blecube/PCB-Design/images/PCB Design - Adapter Card - Copper Top.png

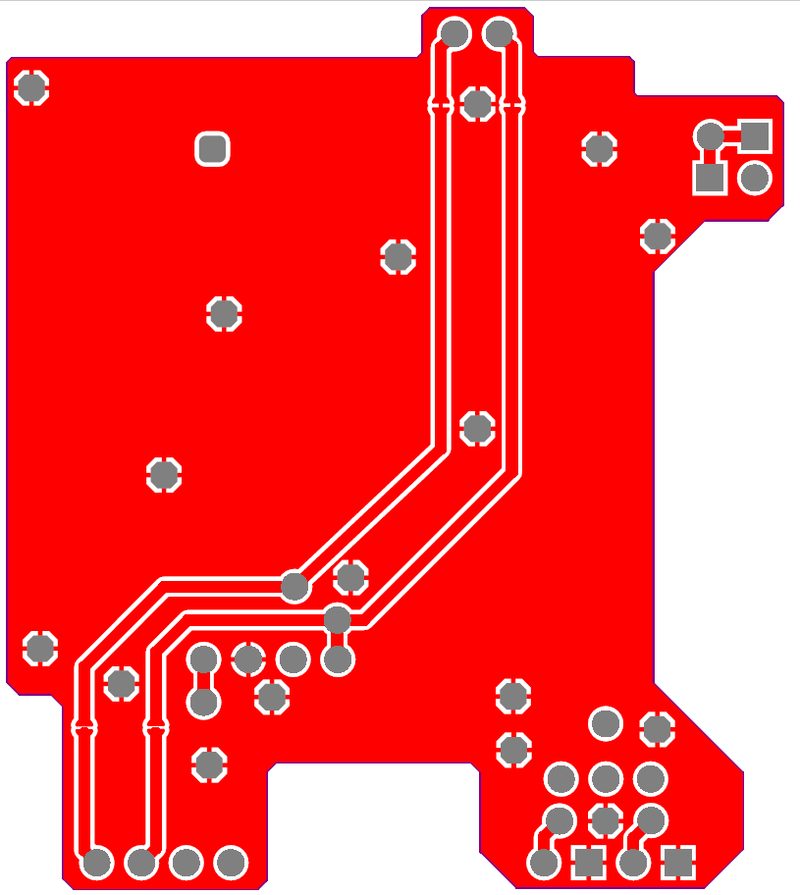
images/PCB Design - Adapter Card - Copper Top.png
