blecube/PCB-Design/images/PCB Design - Adapter Card.png

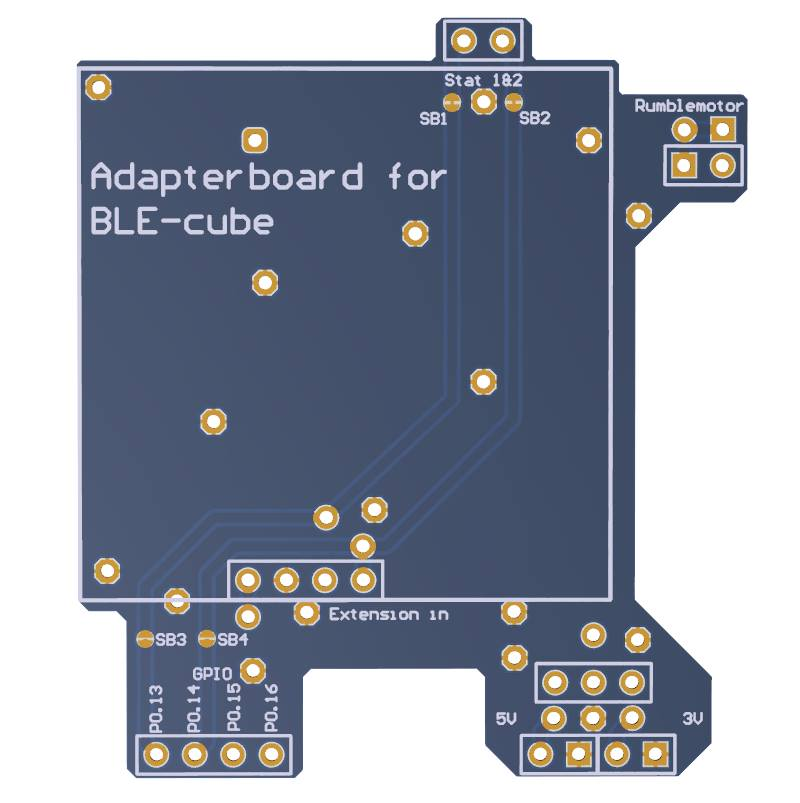
images/PCB Design - Adapter Card.png
