blecube/PCB-Design/images/PCB Design - BLE Card - 3D - Bottom.png

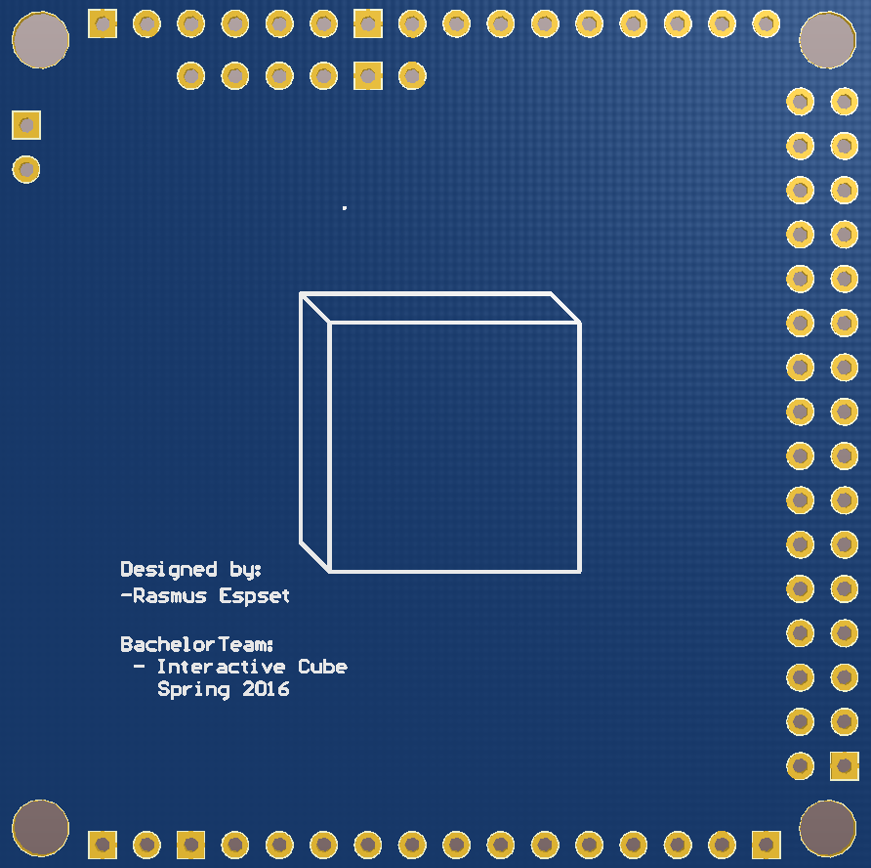
images/PCB Design - BLE Card - 3D - Bottom.png
