blecube/PCB-Design/images/PCB Design - BLE Card - 3D - Copper Bottom.png

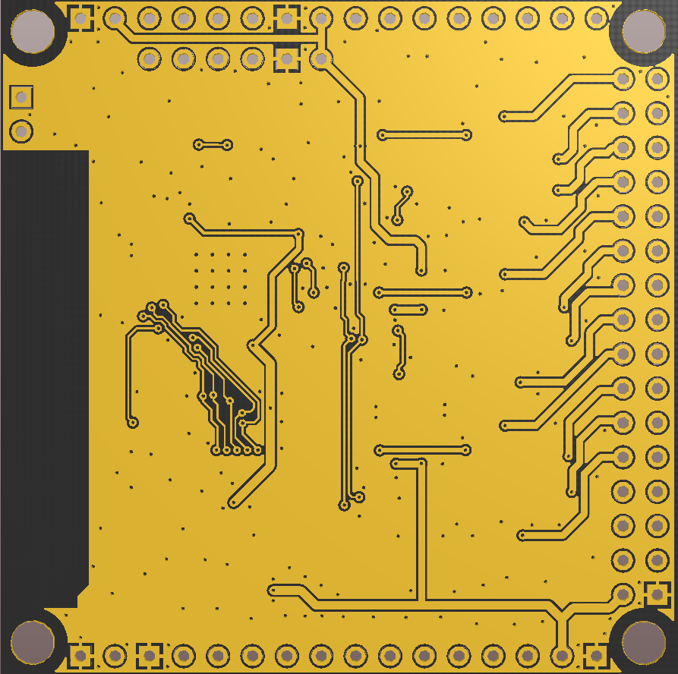
images/PCB Design - BLE Card - 3D - Copper Bottom.png
