blecube/PCB-Design/images/PCB Design - BLE Card.png

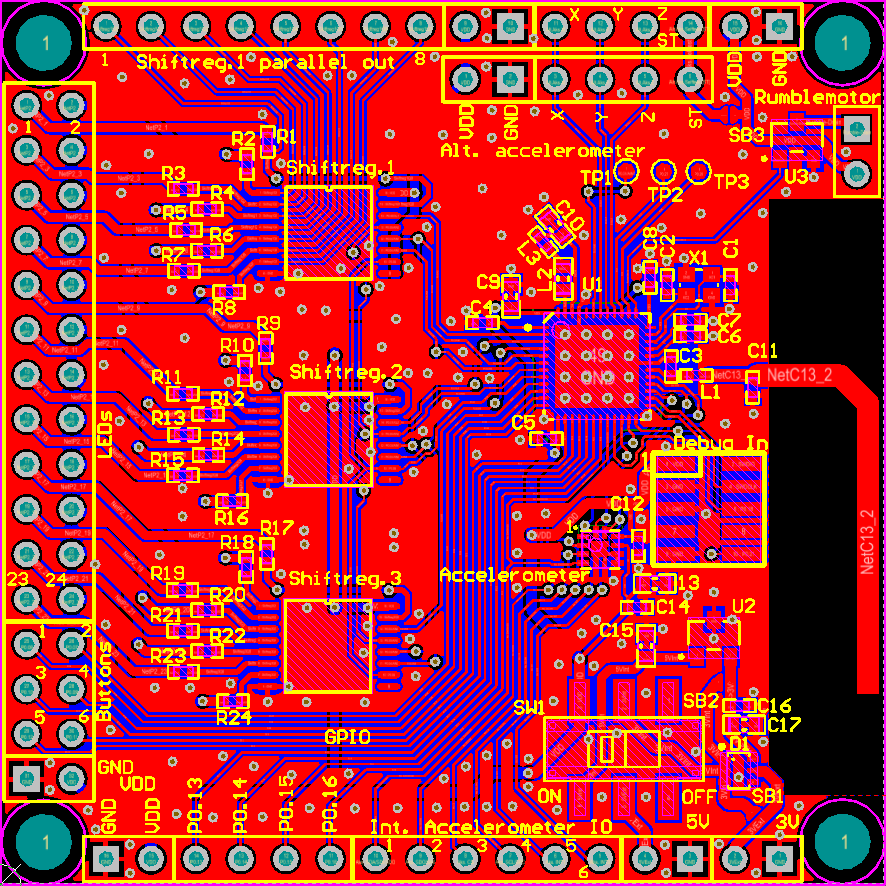
images/PCB Design - BLE Card.png
