blecube/PCB-Design/images/Pinmap BLE-cube.PNG

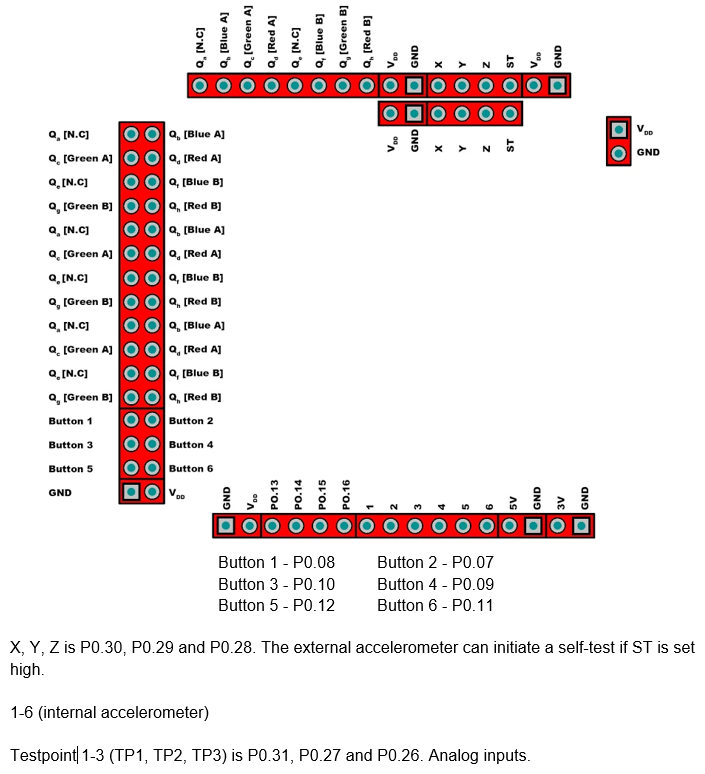
images/Pinmap BLE-cube.PNG
